josephbwalters/SASS/design_artifacts/original/oc_state_transition_diagram.jpg

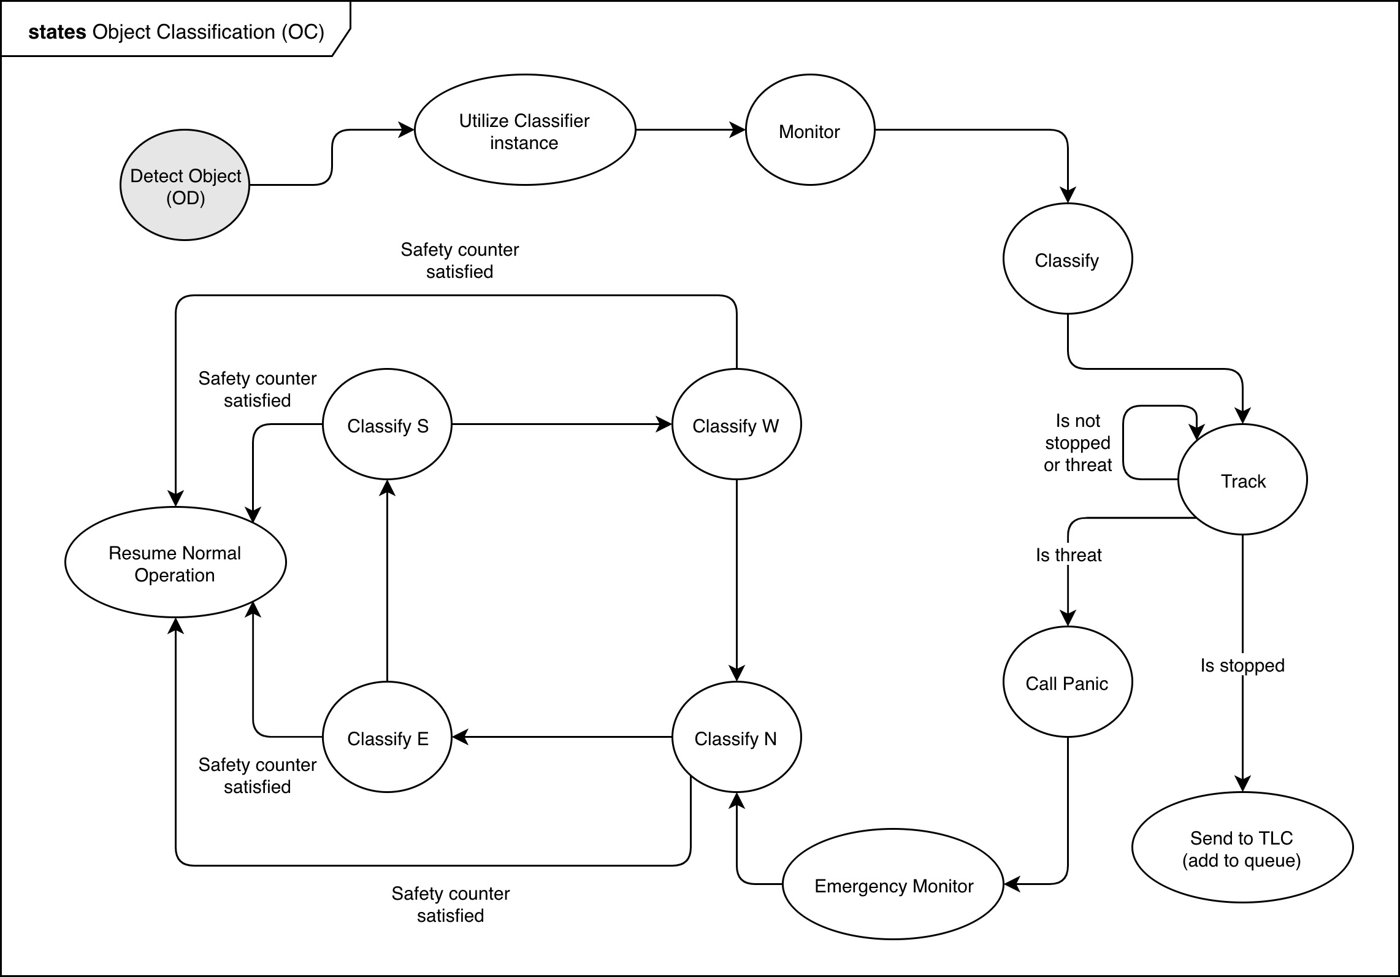
design_artifacts/original/oc_state_transition_diagram.jpg
