josephbwalters/SASS/design_artifacts/original/sass_sequence_diagram.jpg

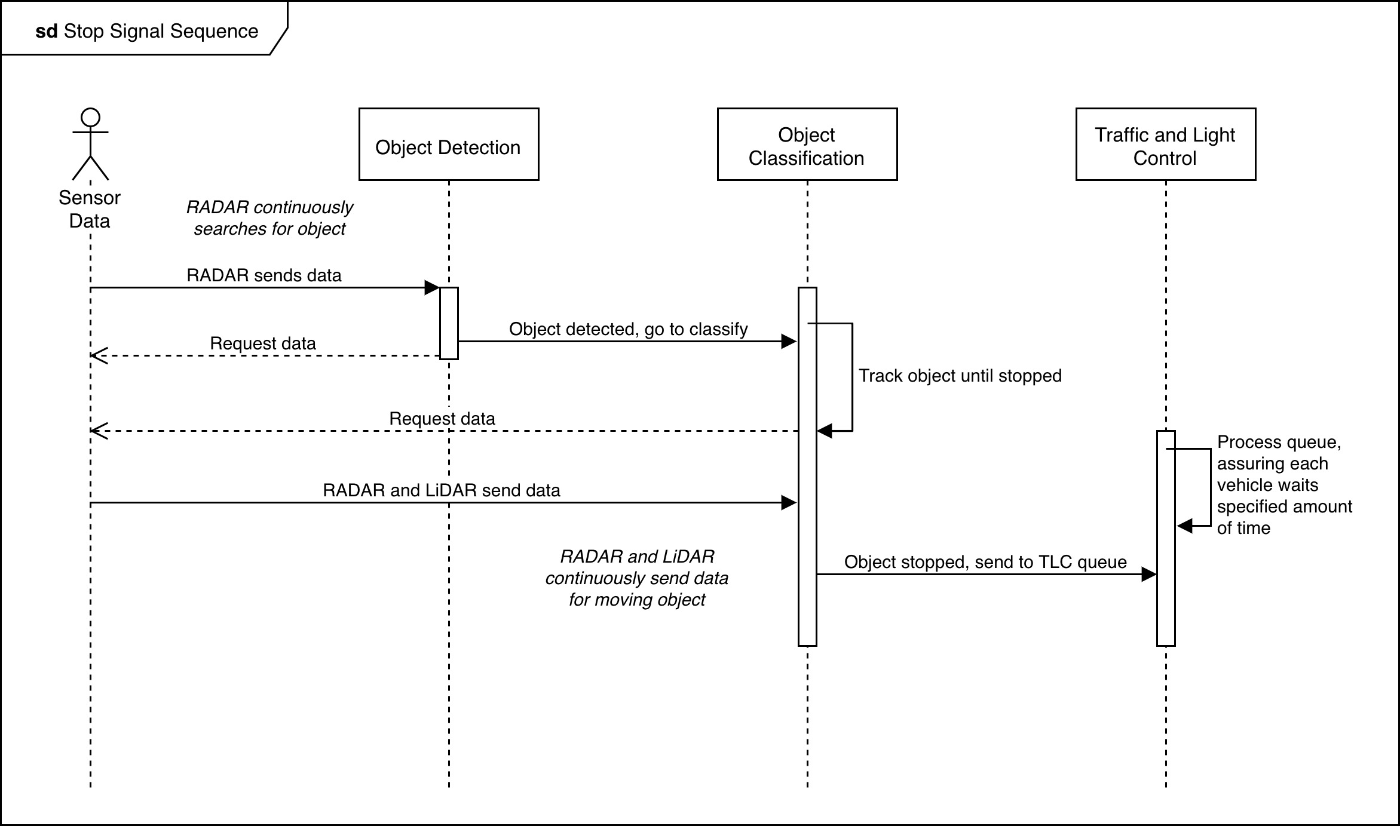
design_artifacts/original/sass_sequence_diagram.jpg
