josephbwalters/SASS/design_artifacts/original/tlc_class_diagram.jpg

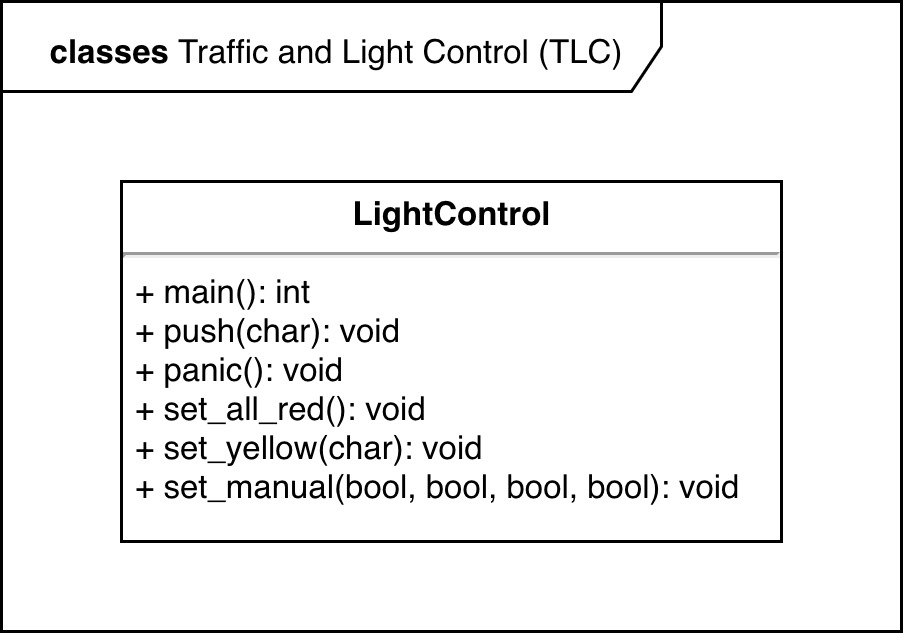
design_artifacts/original/tlc_class_diagram.jpg
