josephbwalters/SASS/design_artifacts/original/tlc_state_transition_diagram.jpg

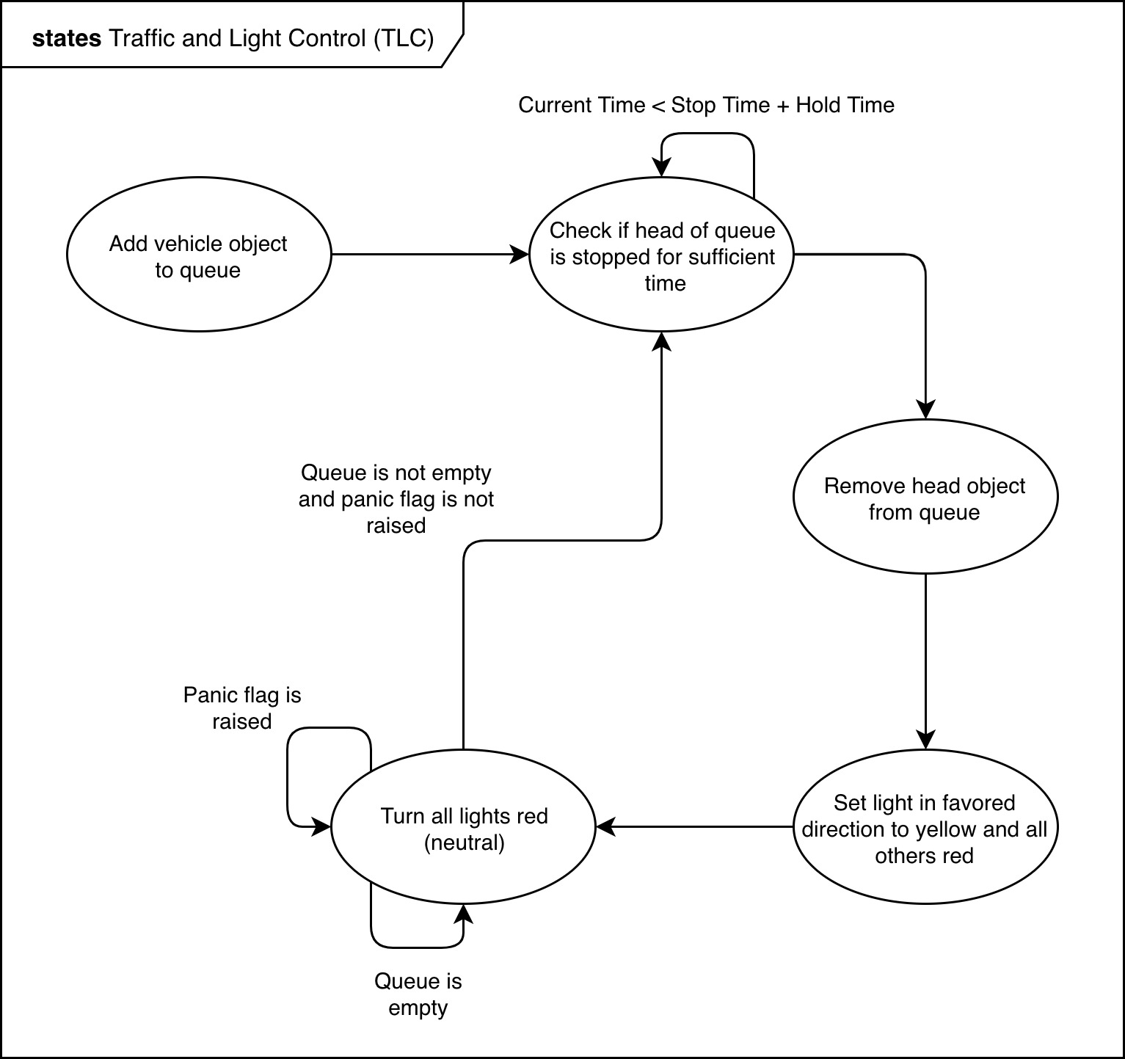
design_artifacts/original/tlc_state_transition_diagram.jpg
