josephbwalters/SASS/design_artifacts/revised/oc_class_diagram.jpg

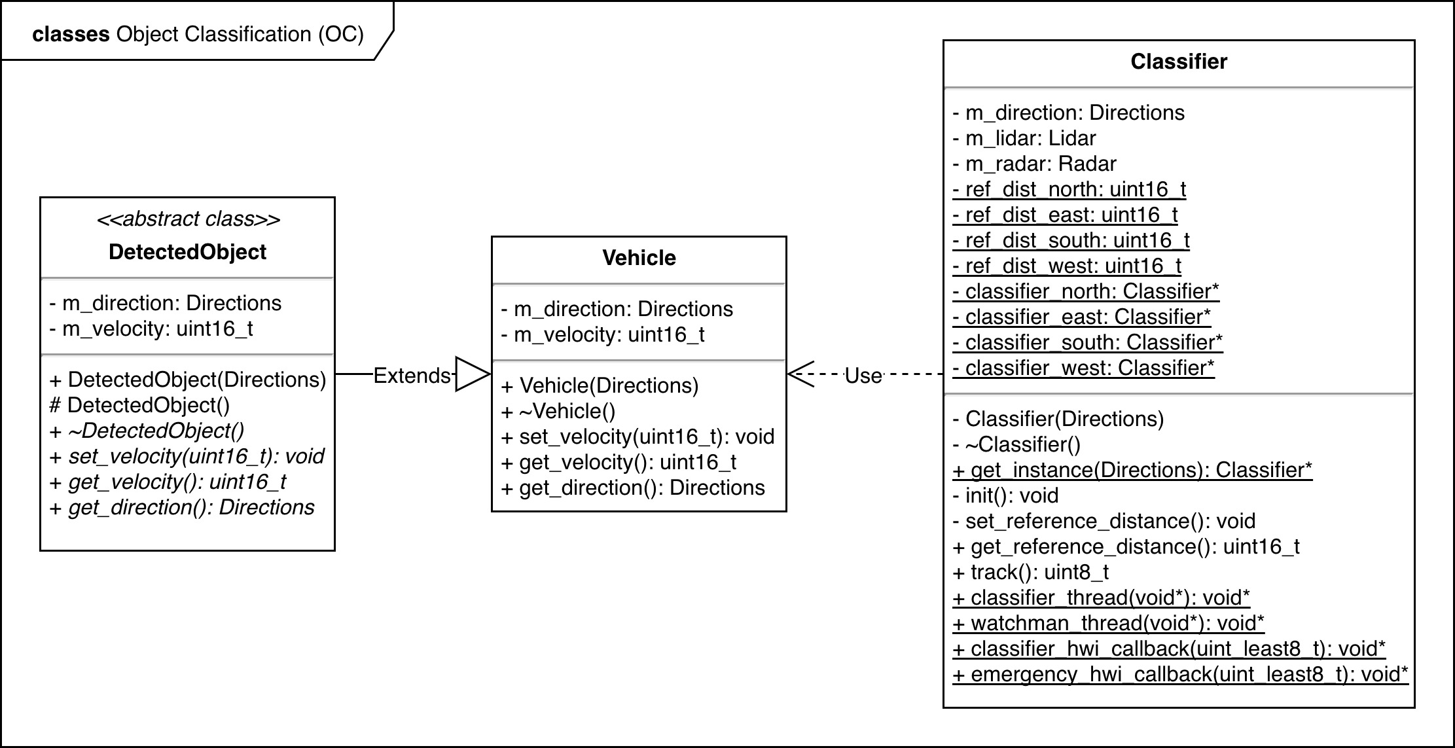
design_artifacts/revised/oc_class_diagram.jpg
