josephbwalters/SASS/design_artifacts/revised/od_oc_state_transition_diagram.jpg

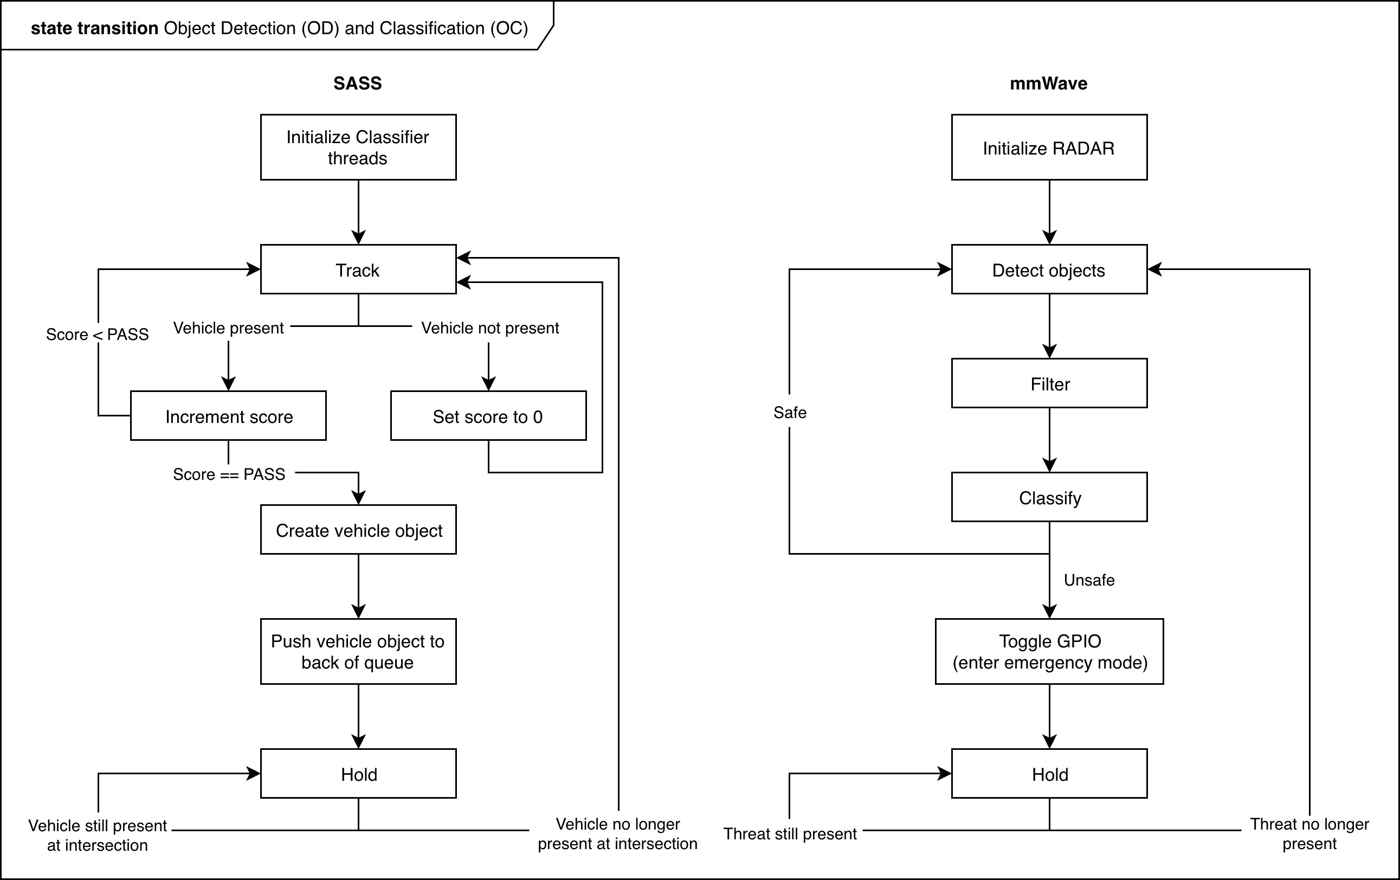
design_artifacts/revised/od_oc_state_transition_diagram.jpg
