josephbwalters/SASS/design_artifacts/revised/sass_large_class_diagram.jpg

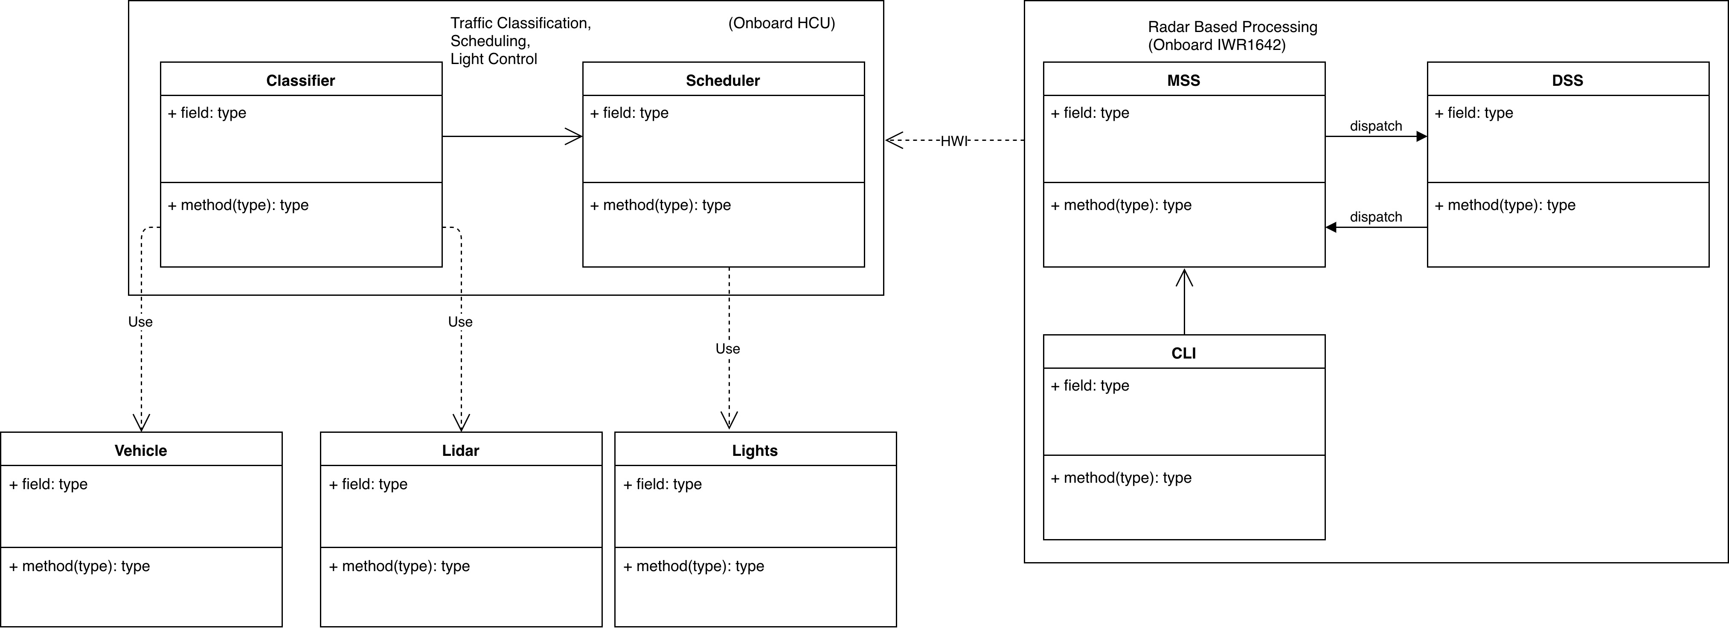
design_artifacts/revised/sass_large_class_diagram.jpg
