josephbwalters/SASS/design_artifacts/revised/sass_sequence_diagram.jpg

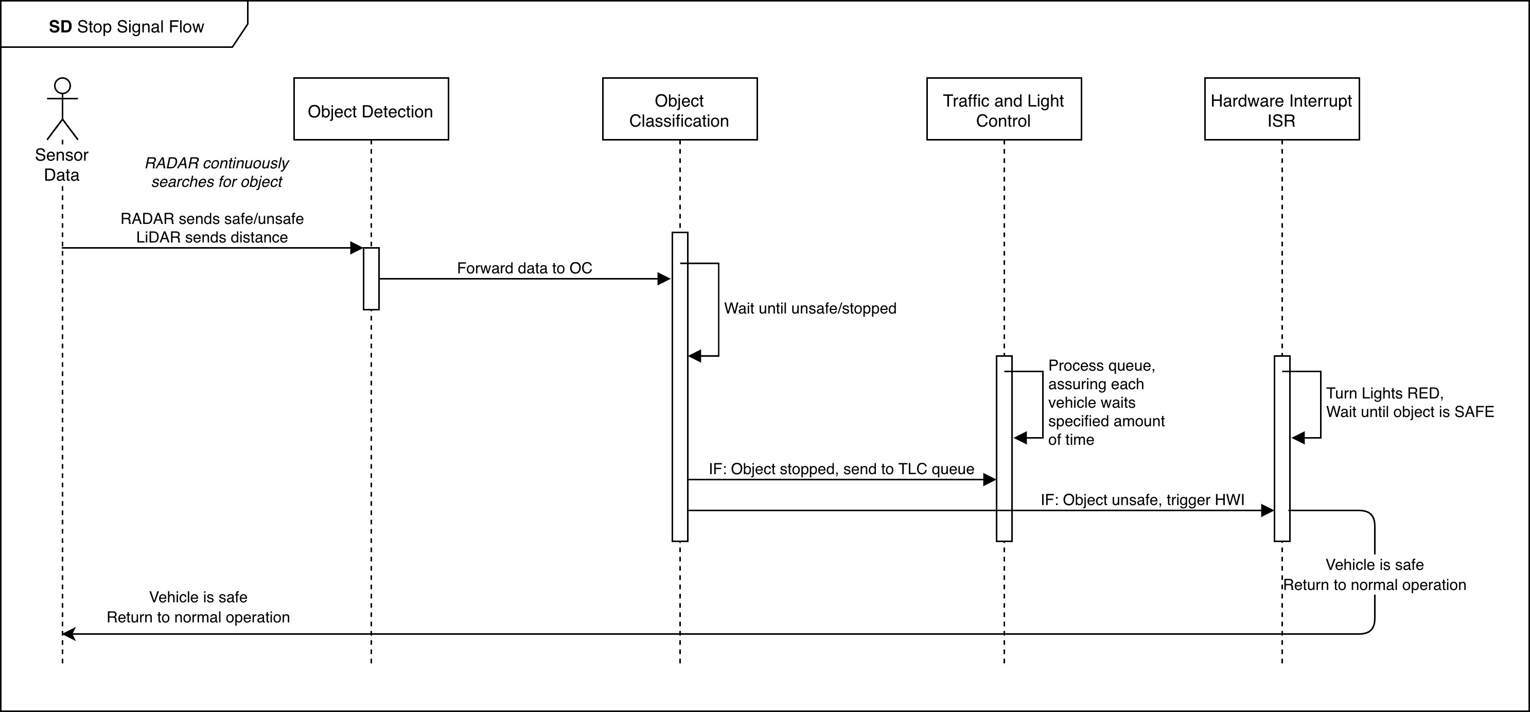
design_artifacts/revised/sass_sequence_diagram.jpg
