josephbwalters/SASS/design_artifacts/revised/tlc_class_diagram.jpg

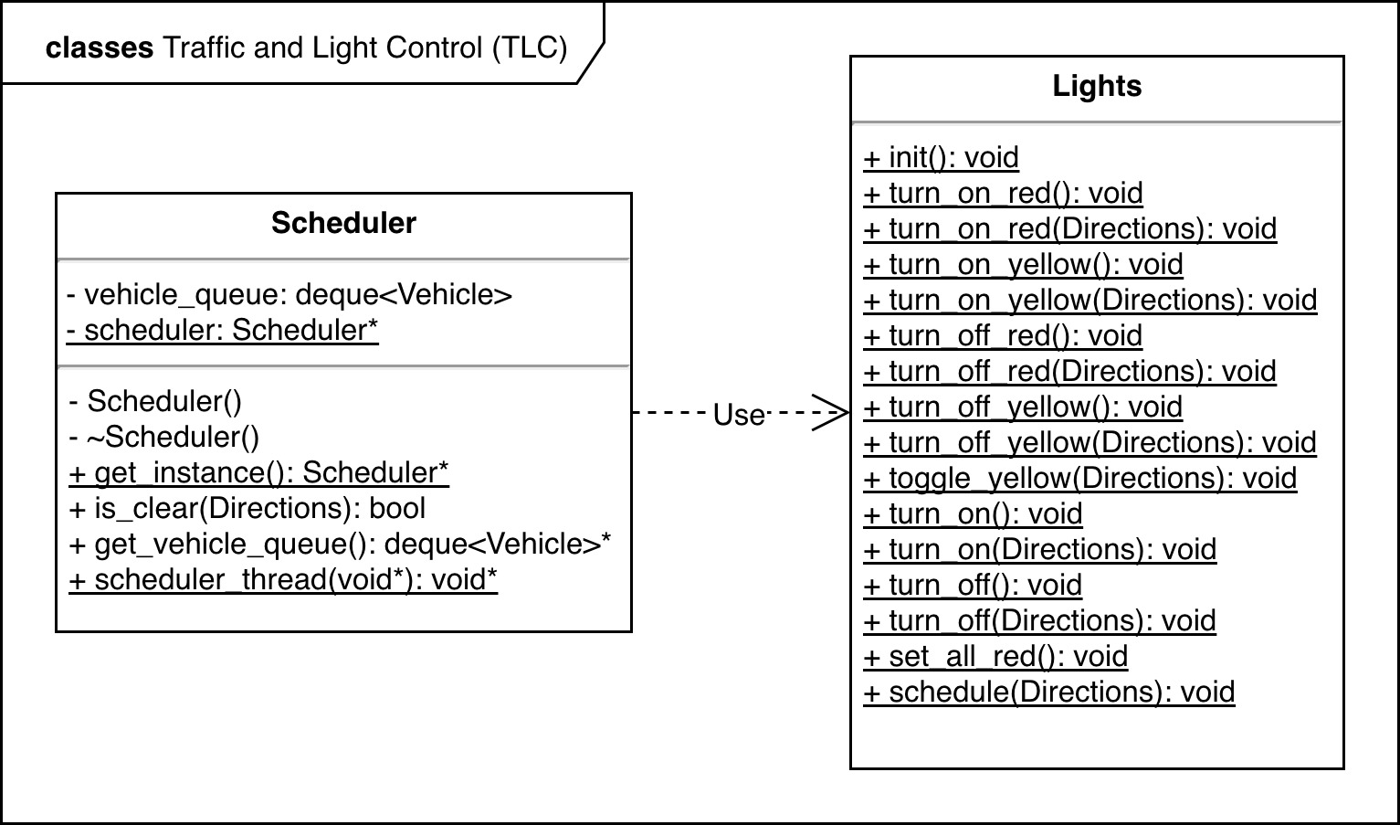
design_artifacts/revised/tlc_class_diagram.jpg
