josephbwalters/SASS/design_artifacts/revised/tlc_state_transition_diagram.jpg

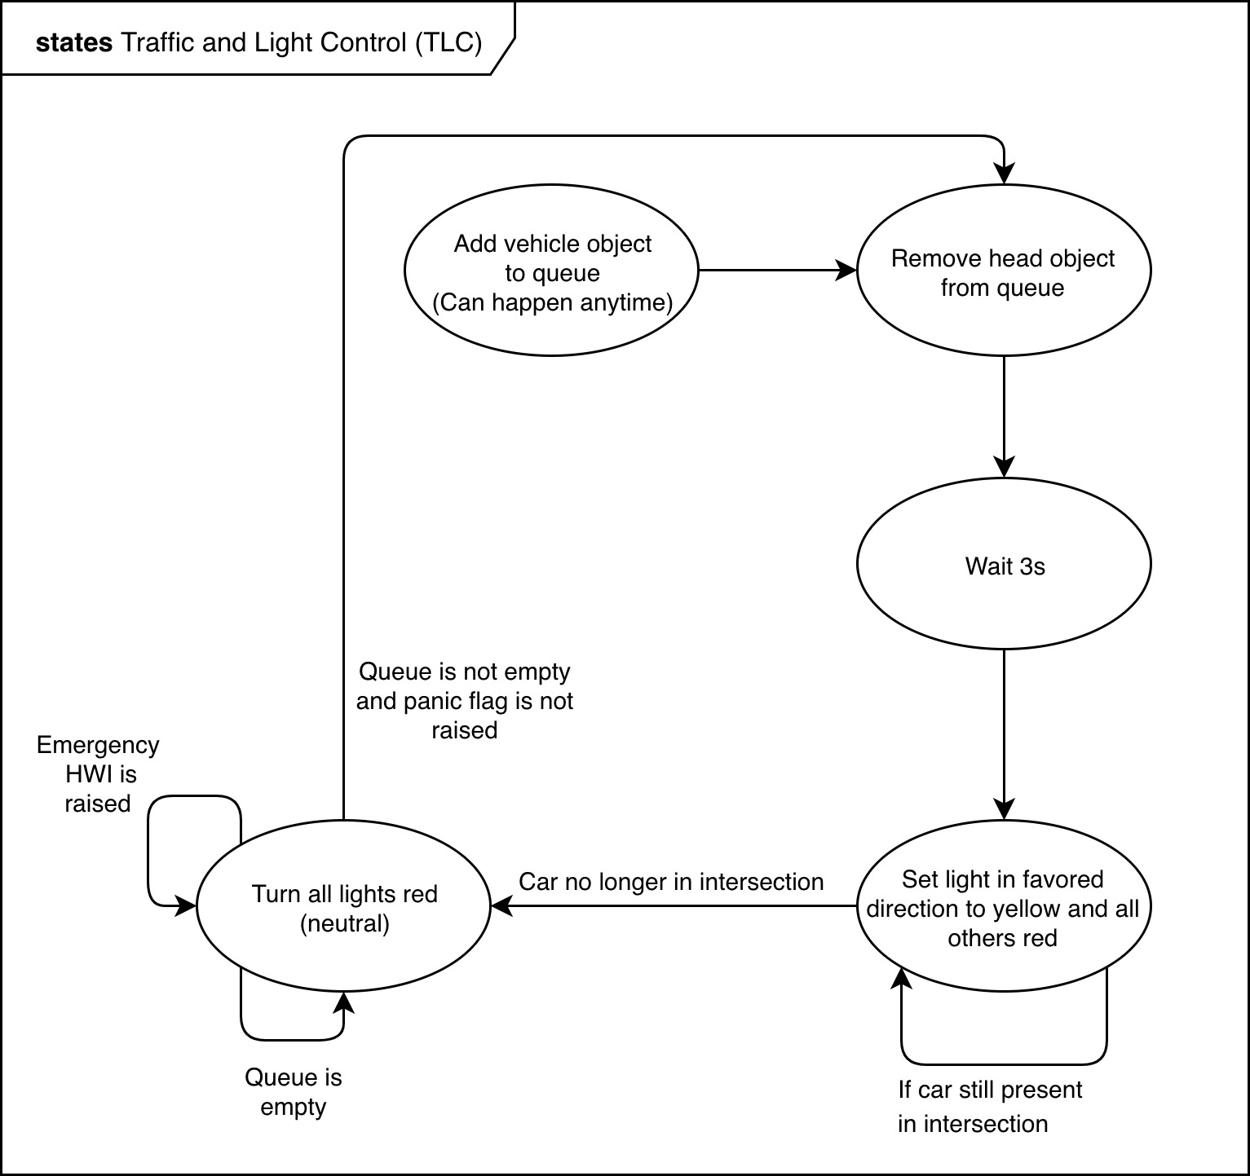
design_artifacts/revised/tlc_state_transition_diagram.jpg
