josephbwalters/SASS/docs/img/BeingBored.JPG

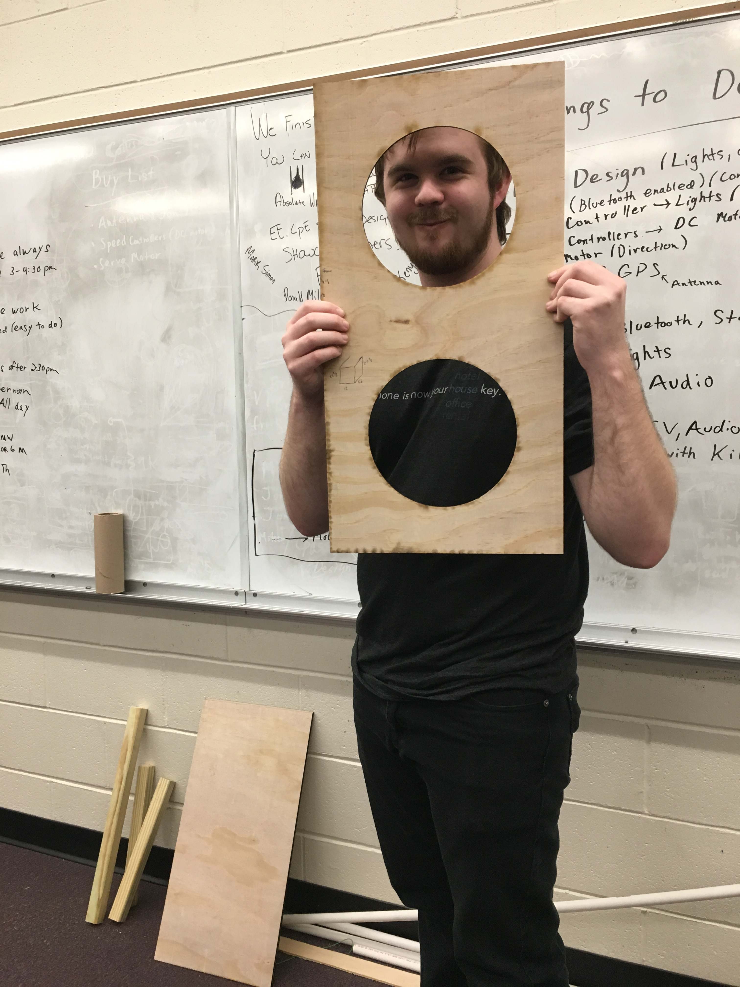
docs/img/BeingBored.JPG
