josephbwalters/SASS/docs/img/DuringDemo.jpg

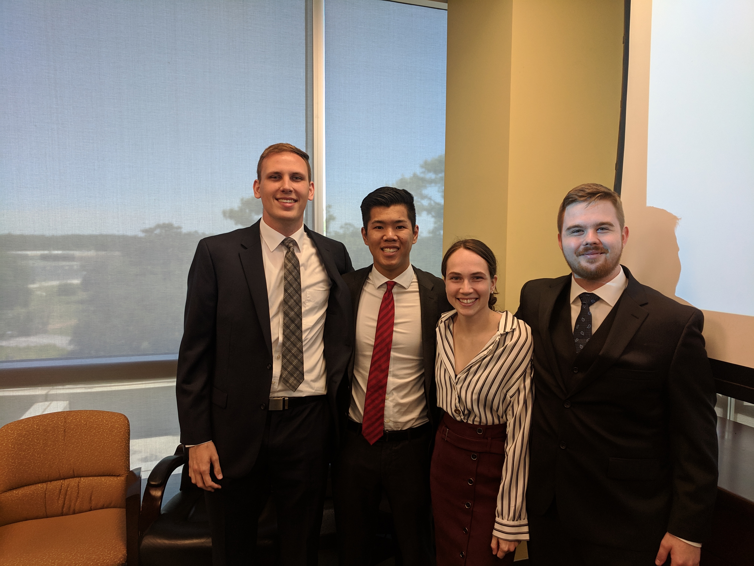
docs/img/DuringDemo.jpg
