josephbwalters/SASS/docs/img/DuringDemoGroupNum.jpg

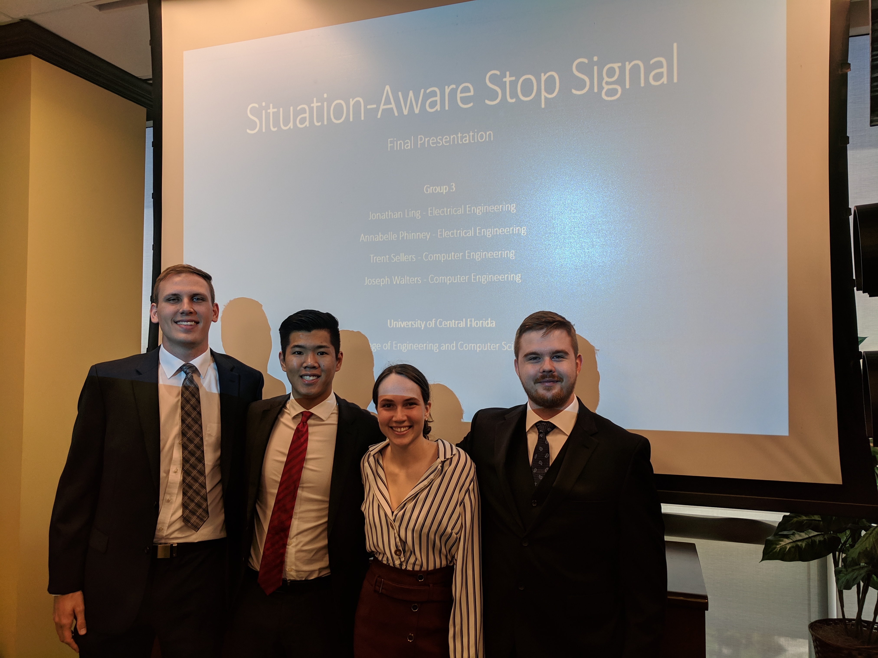
docs/img/DuringDemoGroupNum.jpg
