josephbwalters/SASS/docs/img/Motivation1.JPG

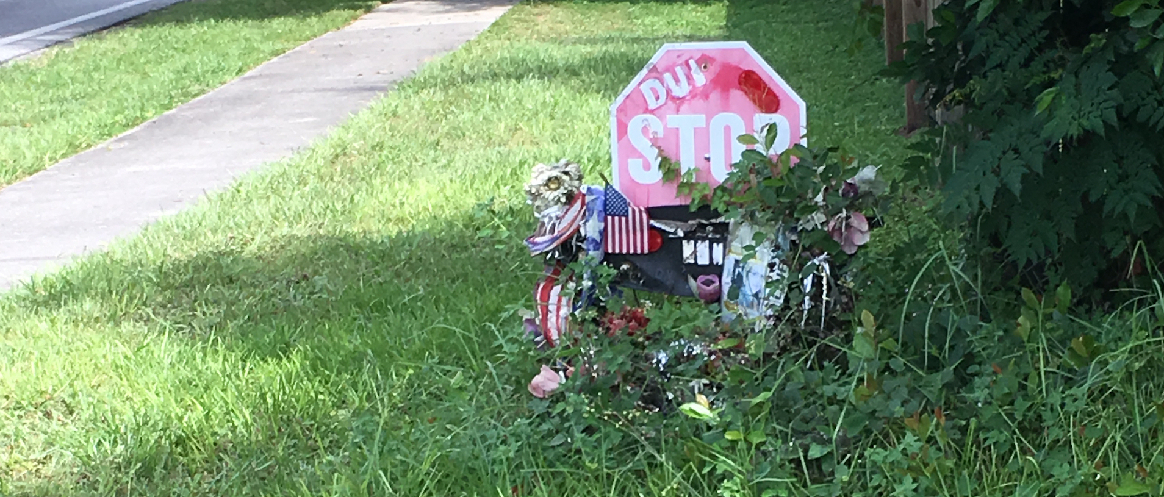
docs/img/Motivation1.JPG
