josephbwalters/SASS/docs/img/pcb_family.JPG

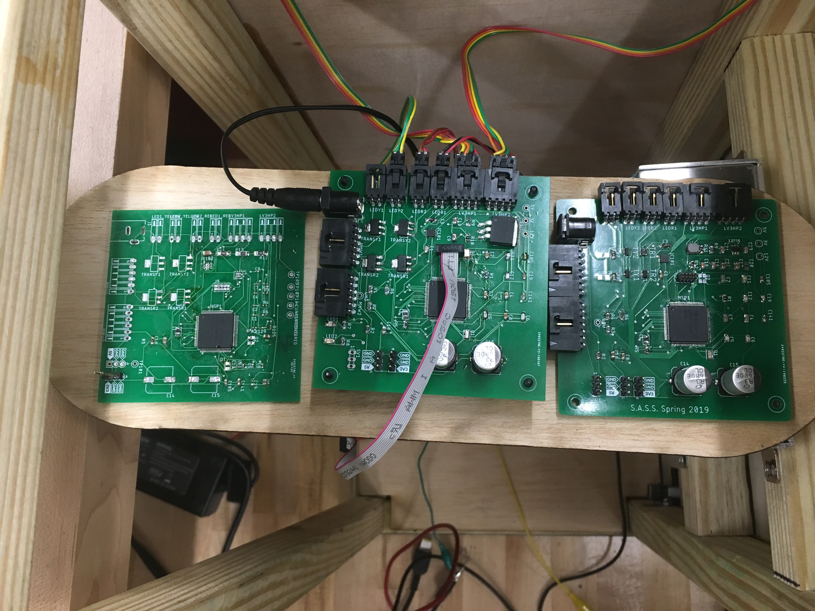
docs/img/pcb_family.JPG
