josephbwalters/SASS/docs/img/shared/signal_upright_outside.JPG

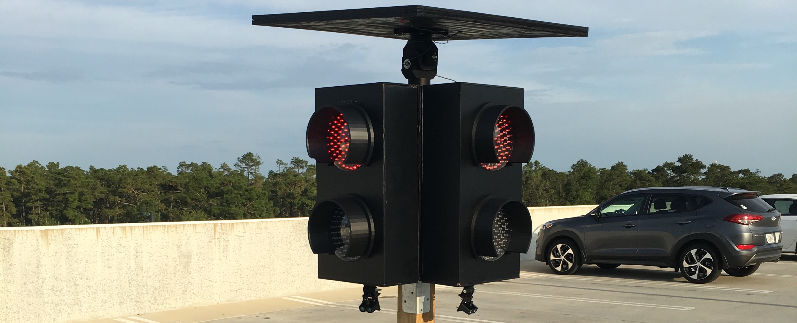
docs/img/shared/signal_upright_outside.JPG
