josephbwalters/SASS/docs/img/team/Annabelle_Phinney_cropped.jpg

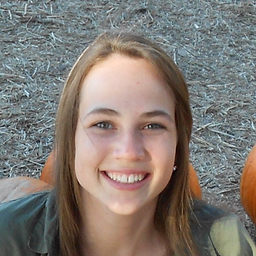
docs/img/team/Annabelle_Phinney_cropped.jpg
