josephbwalters/SASS/docs/img/team/Jon_Ling_cropped.jpg

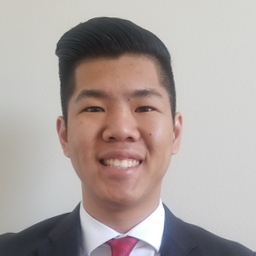
docs/img/team/Jon_Ling_cropped.jpg
