josephbwalters/SASS/docs/img/team/Joseph_Walters_cropped.jpg

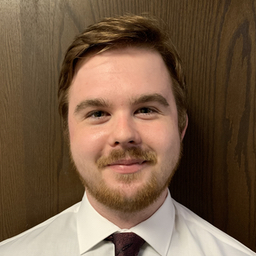
docs/img/team/Joseph_Walters_cropped.jpg
