josephbwalters/SASS/docs/img/team/Trent_Sellers_cropped.jpg

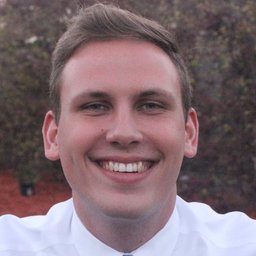
docs/img/team/Trent_Sellers_cropped.jpg
