josephbwalters/SASS/design_artifacts/original/sass_component_diagram.jpg

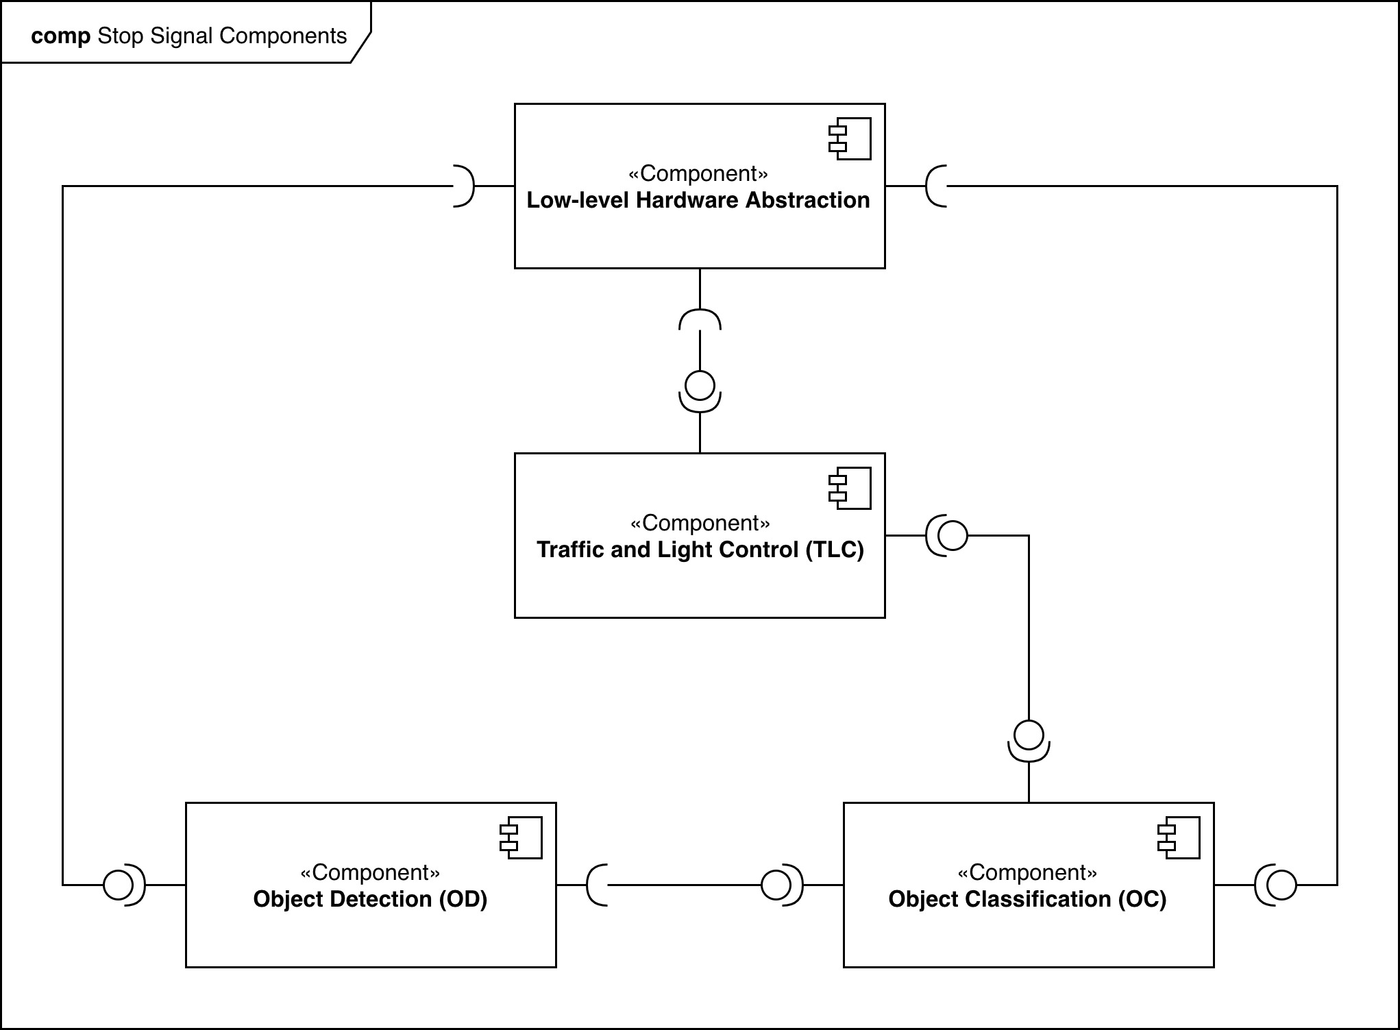
design_artifacts/original/sass_component_diagram.jpg
