josephbwalters/SASS/docs/img/radar_testing.JPG

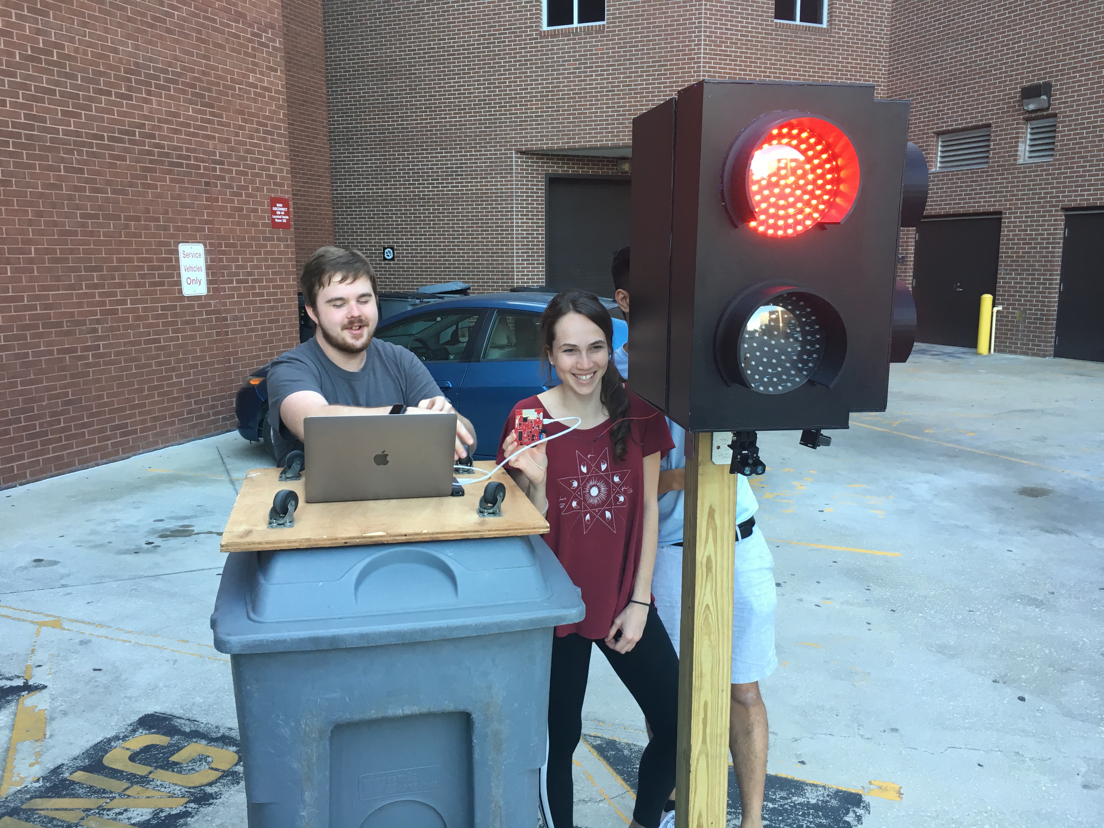
docs/img/radar_testing.JPG
