josephbwalters/SASS/docs/img/SolarPanelTesting.JPG

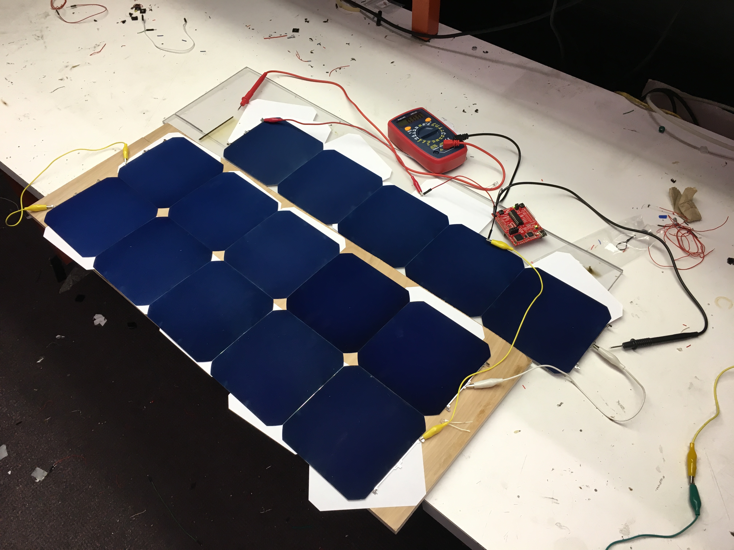
docs/img/SolarPanelTesting.JPG
