josephbwalters/SASS/SASS/MSP_EXP432P401R.h

/*
 * Copyright (c) 2015-2018, Texas Instruments Incorporated
 * All rights reserved.
 *
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
 * *  Redistributions of source code must retain the above copyright
 *    notice, this list of conditions and the following disclaimer.
 *
 * *  Redistributions in binary form must reproduce the above copyright
 *    notice, this list of conditions and the following disclaimer in the
 *    documentation and/or other materials provided with the distribution.
 *
 * *  Neither the name of Texas Instruments Incorporated nor the names of
 *    its contributors may be used to endorse or promote products derived
 *    from this software without specific prior written permission.
 *
 * THIS SOFTWARE IS PROVIDED BY THE COPYRIGHT HOLDERS AND CONTRIBUTORS "AS IS"
 * AND ANY EXPRESS OR IMPLIED WARRANTIES, INCLUDING, BUT NOT LIMITED TO,
 * THE IMPLIED WARRANTIES OF MERCHANTABILITY AND FITNESS FOR A PARTICULAR
 * PURPOSE ARE DISCLAIMED. IN NO EVENT SHALL THE COPYRIGHT OWNER OR
 * CONTRIBUTORS BE LIABLE FOR ANY DIRECT, INDIRECT, INCIDENTAL, SPECIAL,
 * EXEMPLARY, OR CONSEQUENTIAL DAMAGES (INCLUDING, BUT NOT LIMITED TO,
 * PROCUREMENT OF SUBSTITUTE GOODS OR SERVICES; LOSS OF USE, DATA, OR PROFITS;
 * OR BUSINESS INTERRUPTION) HOWEVER CAUSED AND ON ANY THEORY OF LIABILITY,
 * WHETHER IN CONTRACT, STRICT LIABILITY, OR TORT (INCLUDING NEGLIGENCE OR
 * OTHERWISE) ARISING IN ANY WAY OUT OF THE USE OF THIS SOFTWARE,
 * EVEN IF ADVISED OF THE POSSIBILITY OF SUCH DAMAGE.
 */
/** ============================================================================
 *  @file       MSP_EXP432P401R.h
 *
 *  @brief      MSP_EXP432P401R Board Specific APIs
 *
 *  The MSP_EXP432P401R header file should be included in an application as
 *  follows:
 *  @code
 *  #include <MSP_EXP432P401R.h>
 *  @endcode
 *
 *  ============================================================================
 */
#ifndef __MSP_EXP432P401R_H
#define __MSP_EXP432P401R_H

#ifdef __cplusplus
extern "C" {
#endif

/* LEDs on MSP_EXP432P401R are active high. */
#define MSP_EXP432P401R_GPIO_LED_OFF (0)
#define MSP_EXP432P401R_GPIO_LED_ON  (1)

/*!
 *  @def    MSP_EXP432P401R_ADCName
 *  @brief  Enum of ADC channels on the MSP_EXP432P401R dev board
 */
typedef enum MSP_EXP432P401R_ADCName {
    MSP_EXP432P401R_ADC0 = 0,
    MSP_EXP432P401R_ADC1,

    MSP_EXP432P401R_ADCCOUNT
} MSP_EXP432P401R_ADCName;

/*!
 *  @def    MSP_EXP432P401R_ADCBufName
 *  @brief  Enum of ADC hardware peripherals on the MSP_EXP432P401R dev board
 */
typedef enum MSP_EXP432P401R_ADCBufName {
    MSP_EXP432P401R_ADCBUF0 = 0,

    MSP_EXP432P401R_ADCBUFCOUNT
} MSP_EXP432P401R_ADCBufName;

/*!
 *  @def    MSP_EXP432P401R_ADCBuf0ChannelName
 *  @brief  Enum of ADCBuf channels on the MSP_EXP432P401R dev board
 */
typedef enum MSP_EXP432P401R_ADCBuf0ChannelName {
    MSP_EXP432P401R_ADCBUF0CHANNEL0 = 0,
    MSP_EXP432P401R_ADCBUF0CHANNEL1,
    MSP_EXP432P401R_ADCBUF0CHANNEL2,
    MSP_EXP432P401R_ADCBUF0CHANNEL3,

    MSP_EXP432P401R_ADCBUF0CHANNELCOUNT
} MSP_EXP432P401R_ADCBuf0ChannelName;

/*!
 *  @def    MSP_EXP432P401R_CaptureName
 *  @brief  Enum of Capture timer names on the MSP_EXP432P401R dev board
 */
typedef enum MSP_EXP432P401R_CaptureName {
    MSP_EXP432P401R_CAPTURE_TA1 = 0,
    MSP_EXP432P401R_CAPTURE_TA2,
    MSP_EXP432P401R_CAPTURE_TA3,

    MSP_EXP432P401R_CAPTURECOUNT
} MSP_EXP432P401R_CaptureName;

/*!
 *  @def    MSP_EXP432P401R_GPIOName
 *  @brief  Enum of GPIO names on the MSP_EXP432P401R dev board
 */
typedef enum MSP_EXP432P401R_GPIOName {
    MSP_EXP432P401R_GPIO_S1 = 0,
    MSP_EXP432P401R_GPIO_S2,
    MSP_EXP432P401R_SPI_MASTER_READY,
    MSP_EXP432P401R_SPI_SLAVE_READY,
    MSP_EXP432P401R_GPIO_LED1,
    MSP_EXP432P401R_GPIO_LED_RED,
    /*
     * MSP_EXP432P401R_GPIO_LED_GREEN & MSP_EXP432P401R_GPIO_LED_BLUE are used for
     * PWM examples.  Uncomment the following lines if you would like to control
     * the LEDs with the GPIO driver.
     */
    /* MSP_EXP432P401R_GPIO_LED_GREEN, */
    /* MSP_EXP432P401R_GPIO_LED_BLUE, */

    MSP_EXP432P401R_GPIO_TMP116_EN,

    /*
     * MSP_EXP432P401R_SPI_CS1 is used to control chip select pin for slave1
     * MSP_EXP432P401R_SPI_CS2 is used to control chip select pin for slave2
     */
    MSP_EXP432P401R_SPI_CS1,
    MSP_EXP432P401R_SPI_CS2,

    MSP_EXP432P401R_SDSPI_CS,

    /* Sharp LCD Pins */
    MSP_EXP432P401R_LCD_CS,
    MSP_EXP432P401R_LCD_POWER,
    MSP_EXP432P401R_LCD_ENABLE,

    /* SASS-specific configuration - MMW 1 */
    MSP_EXP432P401R_GPIO_MMW1,
    /* SASS-specific configuration - MMW 2 */
    MSP_EXP432P401R_GPIO_MMW2,

    MSP_EXP432P401R_GPIOCOUNT
} MSP_EXP432P401R_GPIOName;

/*!
 *  @def    MSP_EXP432P401R_I2CName
 *  @brief  Enum of I2C names on the MSP_EXP432P401R dev board
 */
typedef enum MSP_EXP432P401R_I2CName {
    MSP_EXP432P401R_I2CB0 = 0,
    /* SASS-specific configuration - LV3HP2 2 */
    MSP_EXP432P401R_I2CB1,
    /* SASS-specific configuration - LV3HP2 1 */
    MSP_EXP432P401R_I2CB2,

    MSP_EXP432P401R_I2CCOUNT
} MSP_EXP432P401R_I2CName;

/*!
 *  @def    MSP_EXP432P401R_I2CSlaveName
 *  @brief  Enum of I2CSlave names on the MSP_EXP432P401R dev board
 */
typedef enum MSP_EXP432P401R_I2CSlaveName {
    MSP_EXP432P401R_I2CSLAVEB0 = 0,

    MSP_EXP432P401R_I2CSLAVECOUNT
} MSP_EXP432P401R_I2CSlaveName;

/*!
 *  @def    MSP_EXP432P401R_NVSName
 *  @brief  Enum of NVS names on the MSP_EXP432P401R dev board
 */
typedef enum MSP_EXP432P401R_NVSName {
    MSP_EXP432P401R_NVSMSP4320 = 0,

    MSP_EXP432P401R_NVSCOUNT
} MSP_EXP432P401R_NVSName;


/*!
 *  @def    MSP_EXP432P401R_PWMName
 *  @brief  Enum of PWM names on the MSP_EXP432P401R dev board
 */
typedef enum MSP_EXP432P401R_PWMName {
    MSP_EXP432P401R_PWM_TA1_1 = 0,
    MSP_EXP432P401R_PWM_TA1_2,

    MSP_EXP432P401R_PWMCOUNT
} MSP_EXP432P401R_PWMName;

/*!
 *  @def    MSP_EXP432P401R_SDFatFSName
 *  @brief  Enum of SDFatFS names on the MSP_EXP432P401R dev board
 */
typedef enum MSP_EXP432P401R_SDFatFSName {
    MSP_EXP432P401R_SDFatFS0 = 0,

    MSP_EXP432P401R_SDFatFSCOUNT
} MSP_EXP432P401R_SDFatFSName;

/*!
 *  @def    MSP_EXP432P401R_SDName
 *  @brief  Enum of SD names on the MSP_EXP432P401R dev board
 */
typedef enum MSP_EXP432P401R_SDName {
    MSP_EXP432P401R_SDSPI0 = 0,

    MSP_EXP432P401R_SDCOUNT
} MSP_EXP432P401R_SDName;

/*!
 *  @def    MSP_EXP432P401R_SPIName
 *  @brief  Enum of SPI names on the MSP_EXP432P401R dev board
 */
typedef enum MSP_EXP432P401R_SPIName {
    MSP_EXP432P401R_SPIB0 = 0,
    MSP_EXP432P401R_SPIB2,
    MSP_EXP432P401R_SPIB3,
    MSP_EXP432P401R_SPIB4,
    /* SASS-specific configuration - MMW 1 */
    MSP_EXP432P401R_SPIB5,
    /* SASS-specific configuration - MMW 2 */
    MSP_EXP432P401R_SPIB6,

    MSP_EXP432P401R_SPICOUNT
} MSP_EXP432P401R_SPIName;

/*!
 *  @def    MSP_EXP432P401R_TimerName
 *  @brief  Enum of Timer names on the MSP_EXP432P401R dev board
 */
typedef enum MSP_EXP432P401R_TimerName {
    MSP_EXP432P401R_TIMER_T32_0 = 0,
    MSP_EXP432P401R_TIMER_T32_1,
    MSP_EXP432P401R_TIMER_TA_1,
    MSP_EXP432P401R_TIMER_TA_2,
    MSP_EXP432P401R_TIMER_TA_3,

    MSP_EXP432P401R_TIMERCOUNT
} MSP_EXP432P401R_TimerName;

/*!
 *  @def    MSP_EXP432P401R_UARTName
 *  @brief  Enum of UART names on the MSP_EXP432P401R dev board
 */
typedef enum MSP_EXP432P401R_UARTName {
    MSP_EXP432P401R_UARTA0 = 0,
    MSP_EXP432P401R_UARTA2,

    MSP_EXP432P401R_UARTCOUNT
} MSP_EXP432P401R_UARTName;

/*!
 *  @def    MSP_EXP432P401R_WatchdogName
 *  @brief  Enum of Watchdog names on the MSP_EXP432P401R dev board
 */
typedef enum MSP_EXP432P401R_WatchdogName {
    MSP_EXP432P401R_WATCHDOG = 0,

    MSP_EXP432P401R_WATCHDOGCOUNT
} MSP_EXP432P401R_WatchdogName;

/*!
 *  @brief  Initialize the general board specific settings
 *
 *  This function initializes the general board specific settings.
 */
extern void MSP_EXP432P401R_initGeneral(void);

#ifdef __cplusplus
}
#endif

#endif /* __MSP_EXP432P401R_H */
