josephbwalters/SASS/SASS/Sources/TLC/Scheduler.h

/*
 * Scheduler.h
 * Created by: Joseph Walters, Trent Sellers 
 */

#ifndef SCHEDULER_H_
#define SCHEDULER_H_

/* Standard headers */
#include <deque>

/* POSIX thread support */
#include <pthread.h>

/* SASS-specific headers */
#include <Sources/Directions.h>
#include <Sources/LLHA/Lights/Lights.h>
#include <Sources/LLHA/Sensors/Lidar.h>
#include <Sources/OC/Vehicle.h>

using namespace std;
using namespace sources::llha::lights;
using namespace sources::llha::sensors;
using namespace sources::oc;

namespace sources
{
namespace tlc
{


class Scheduler
{
public:
    static Scheduler* get_instance();

    bool is_clear(Directions direction);
    deque<Vehicle>* get_vehicle_queue();
    pthread_mutex_t* get_queue_mutex();

    // Thread-able method(s)
    static void *scheduler_thread(void *refs);

private:
    Scheduler();
    virtual ~Scheduler();

    deque<Vehicle> vehicle_queue;
    pthread_mutex_t queue_mutex;

    static Scheduler* scheduler;
};


}} // sources::tlc

#endif // SCHEDULER_H_
