josephbwalters/SASS/SASS/Sources/OC/DetectedObject.cpp

/*
 * DetectedObject.cpp
 * Created by: Joseph Walters, Trent Sellers 
 */

/* SASS-specific headers */
#include <Sources/OC/DetectedObject.h>

using namespace sources;
using namespace sources::oc;

DetectedObject::DetectedObject(Directions direction) : m_direction(direction)
{

}

DetectedObject::DetectedObject()
{

}

DetectedObject::~DetectedObject()
{
    // TODO: Clean up (if necessary)
}
